publiclab/Passive-PM/deployment/images/IMG_20151015_120027-trim.png

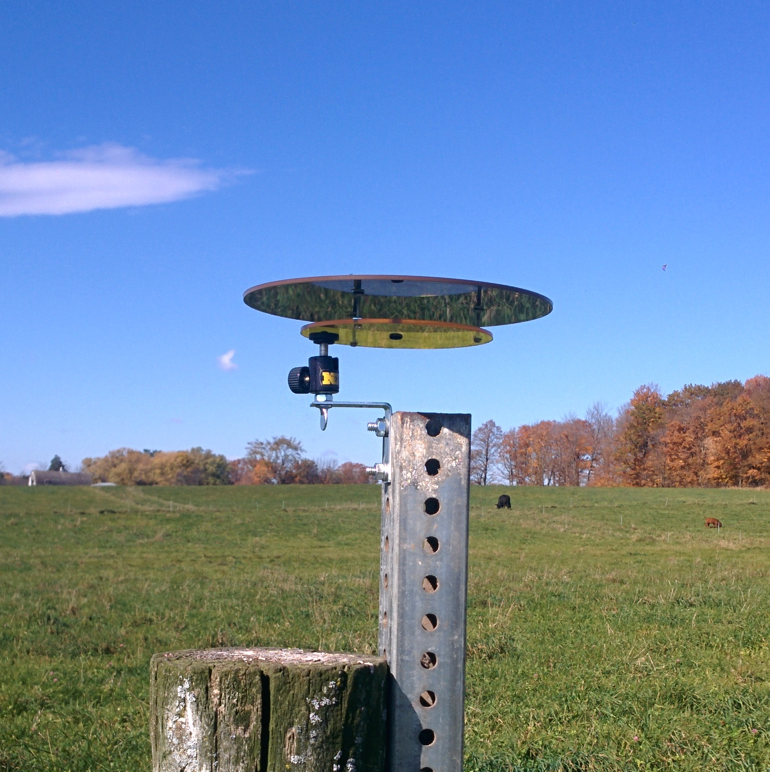
deployment/images/IMG_20151015_120027-trim.png
