publiclab/Passive-PM/deployment/images/IMG_20151026_110609.jpg

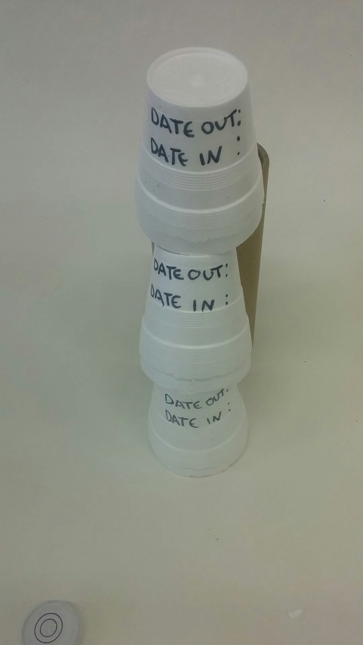
deployment/images/IMG_20151026_110609.jpg
