publiclab/Passive-PM/deployment/images/twobubble.png

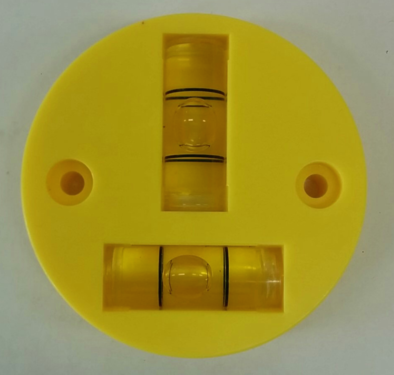
deployment/images/twobubble.png
