publiclab/Passive-PM/microscopy/images/11_2_15_PG2_8_20x.jpg

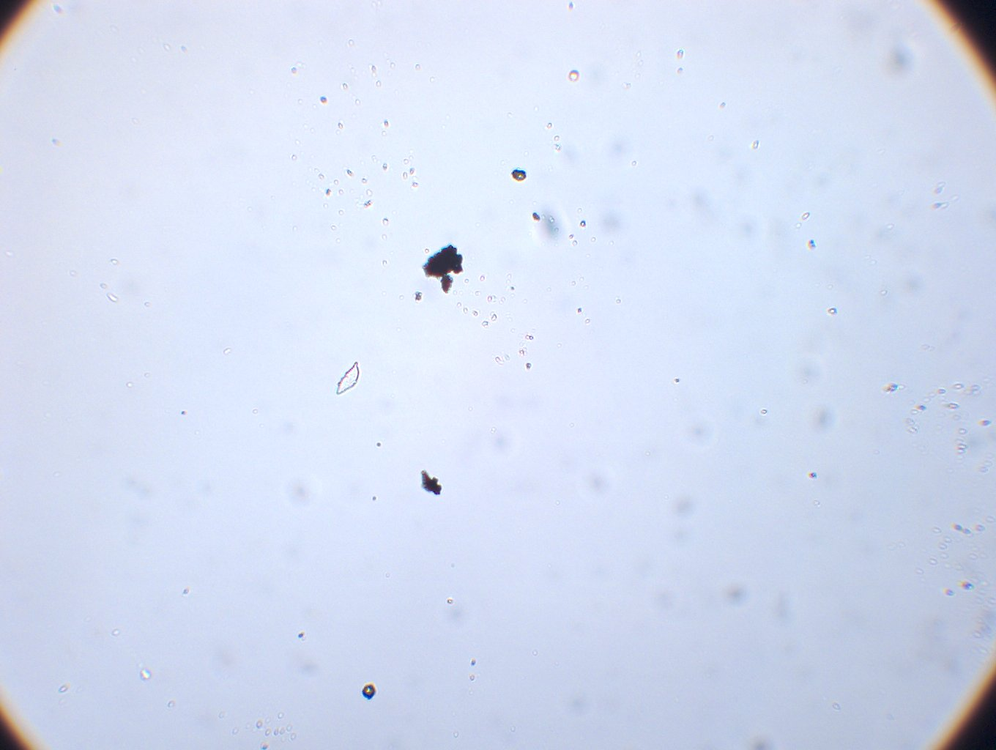
microscopy/images/11_2_15_PG2_8_20x.jpg
