publiclab/Passive-PM/microscopy/images/11_2_15_PG2_8_20x_subtractbackground_bandpass.jpg

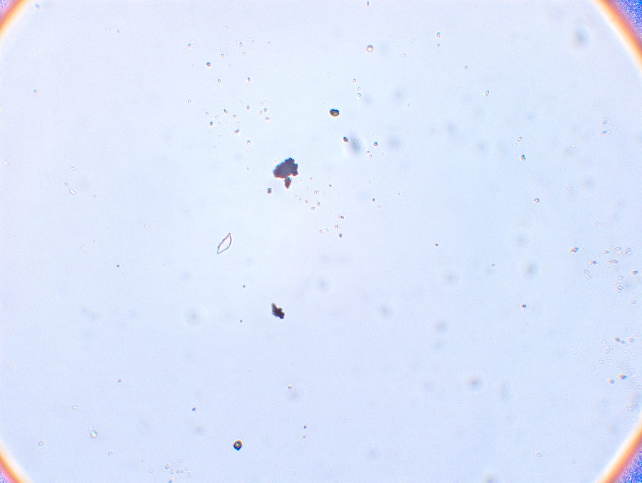
microscopy/images/11_2_15_PG2_8_20x_subtractbackground_bandpass.jpg
