publiclab/Passive-PM/microscopy/images/Dust.gif

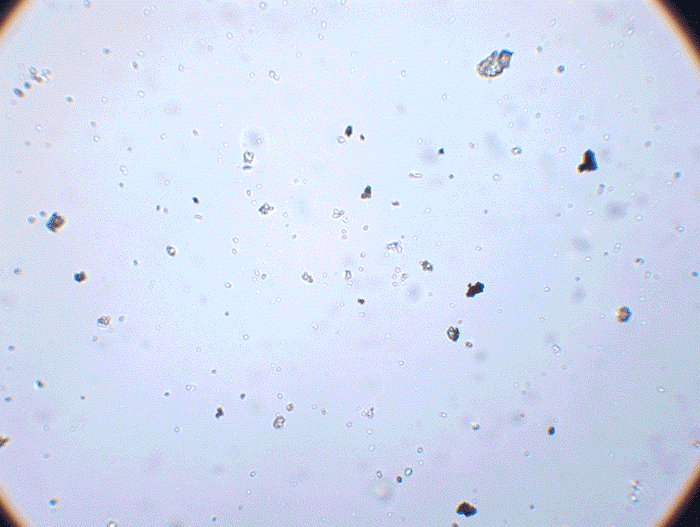
microscopy/images/Dust.gif
