publiclab/Passive-PM/microscopy/images/im_0057_20160612_104109.jpg

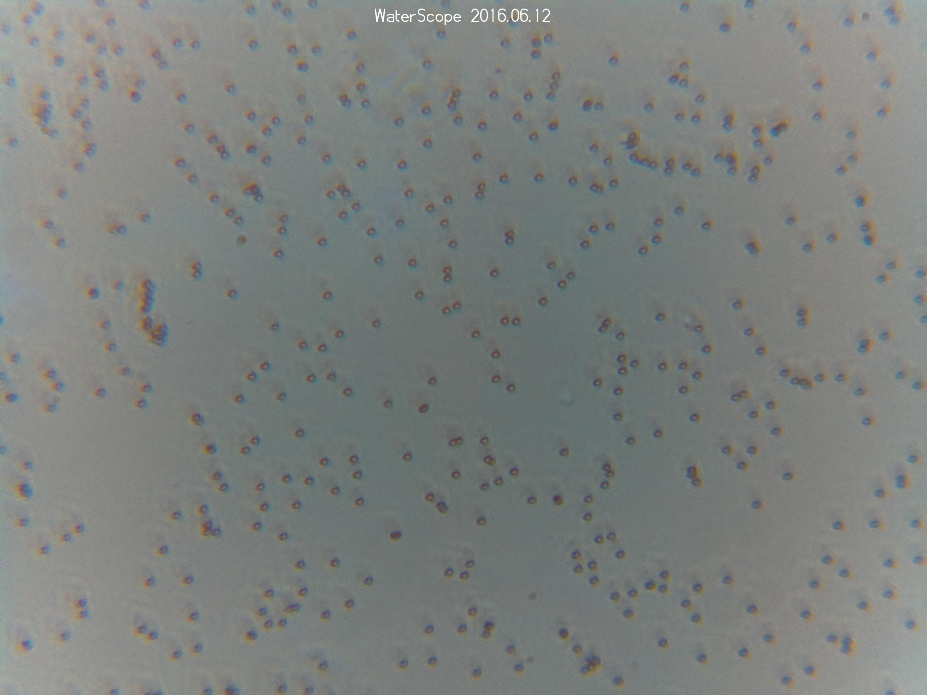
microscopy/images/im_0057_20160612_104109.jpg
