publiclab/Passive-PM/microscopy/images/im_0074_20160613_082013.jpg

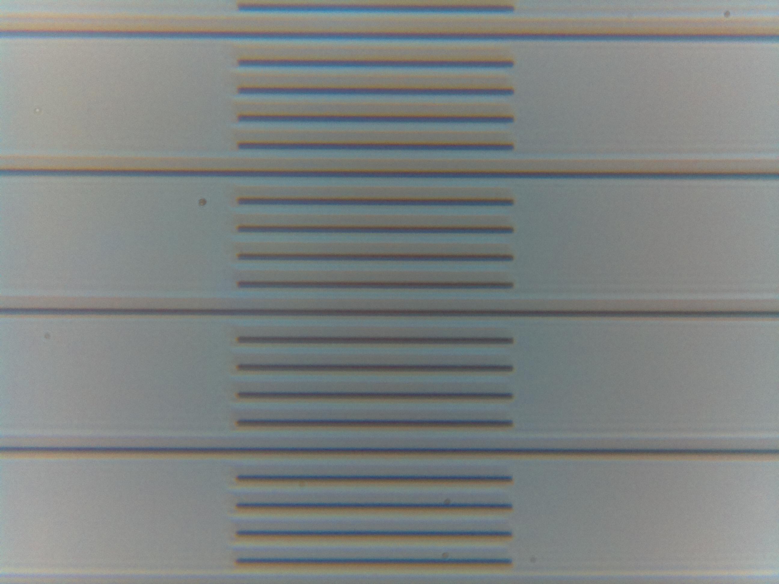
microscopy/images/im_0074_20160613_082013.jpg
