publiclab/Passive-PM/microscopy/images/Screen_Shot_2015-09-18_at_6.32.18_PM.png

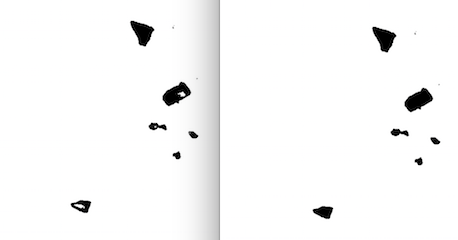
microscopy/images/Screen_Shot_2015-09-18_at_6.32.18_PM.png
