publiclab/Passive-PM/microscopy/images/stable_dust.gif

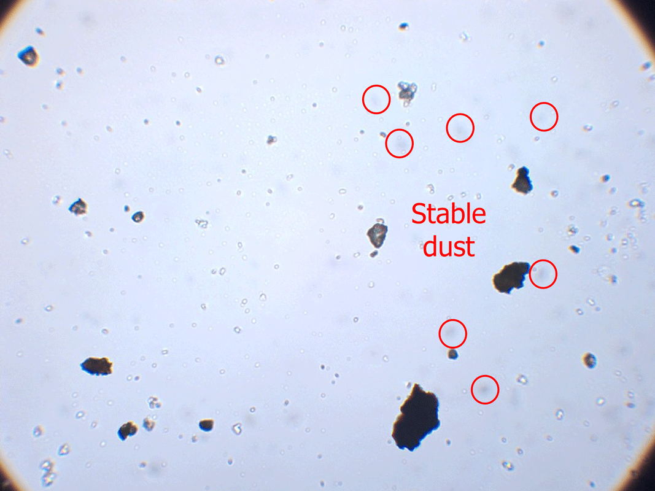
microscopy/images/stable_dust.gif
