publiclab/Passive-PM/microscopy/images/Wi_HA_113015_40x_3.tif

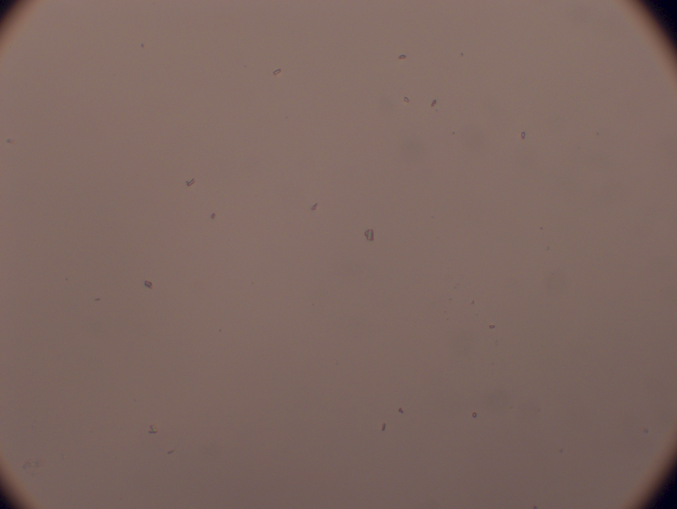
microscopy/images/Wi_HA_113015_40x_3.tif
