publiclab/Passive-PM/monitor/cap-diagram.bmp

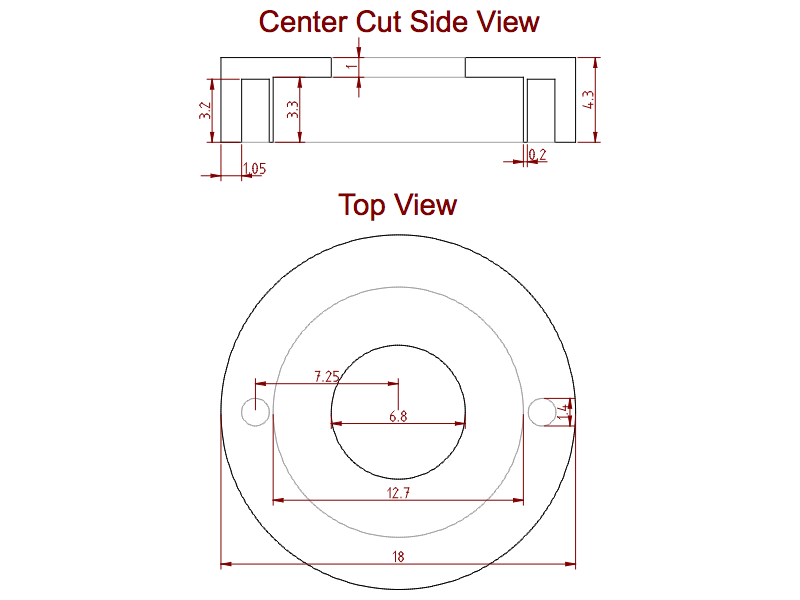
monitor/cap-diagram.bmp
