publiclab/Passive-PM/monitor/images/mesh-hole-area.png

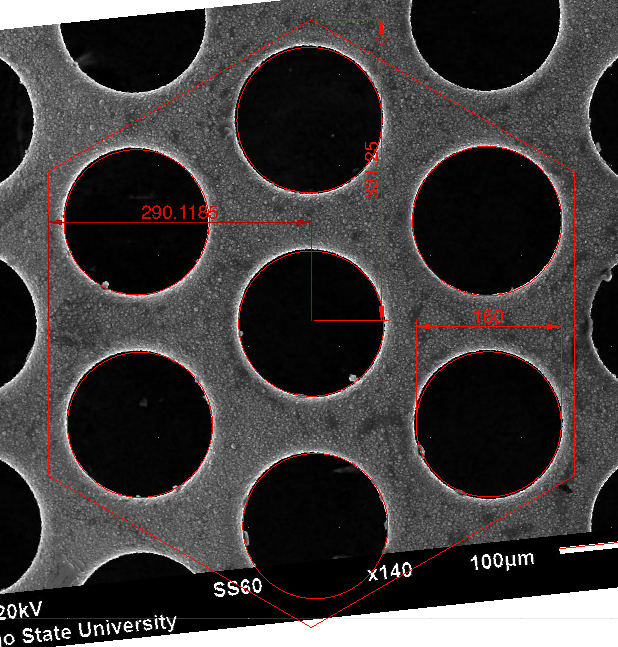
monitor/images/mesh-hole-area.png
