publiclab/Passive-PM/preparation/images/image05.jpg

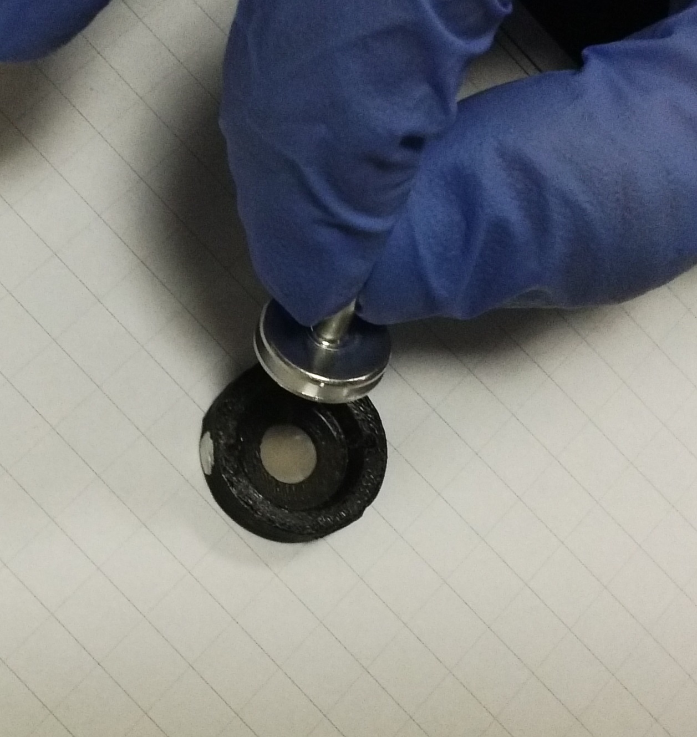
preparation/images/image05.jpg
