publiclab/Passive-PM/preparation/images/image06.jpg

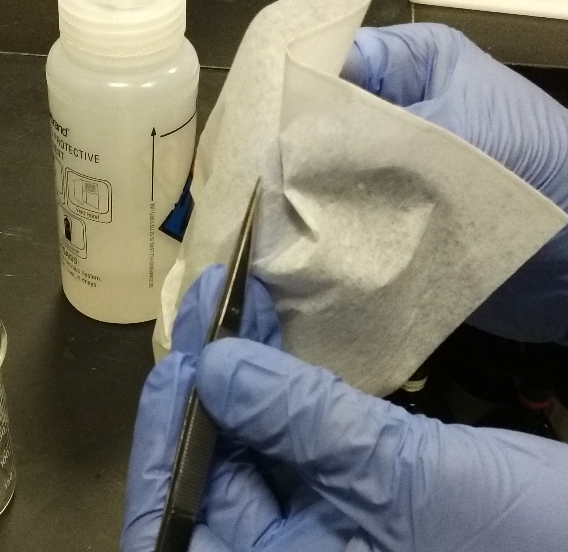
preparation/images/image06.jpg
