publiclab/Passive-PM/preparation/images/image09.jpg

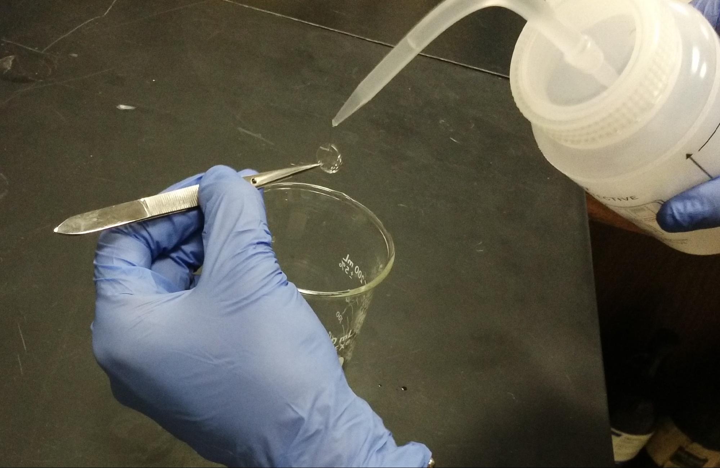
preparation/images/image09.jpg
